KyleSimkus/TinyPowerController/TPC/Default Configuration/Outputs/3D Top Angle.png

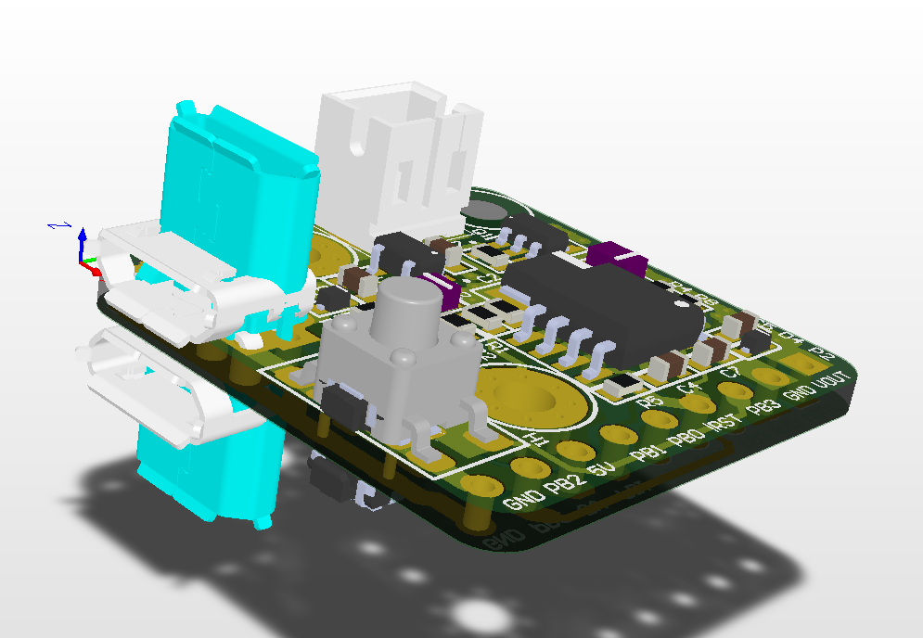
TPC/Default Configuration/Outputs/3D Top Angle.png
