KyleSimkus/TinyPowerController/TPC/Default Configuration/Outputs/3D Bottom.png

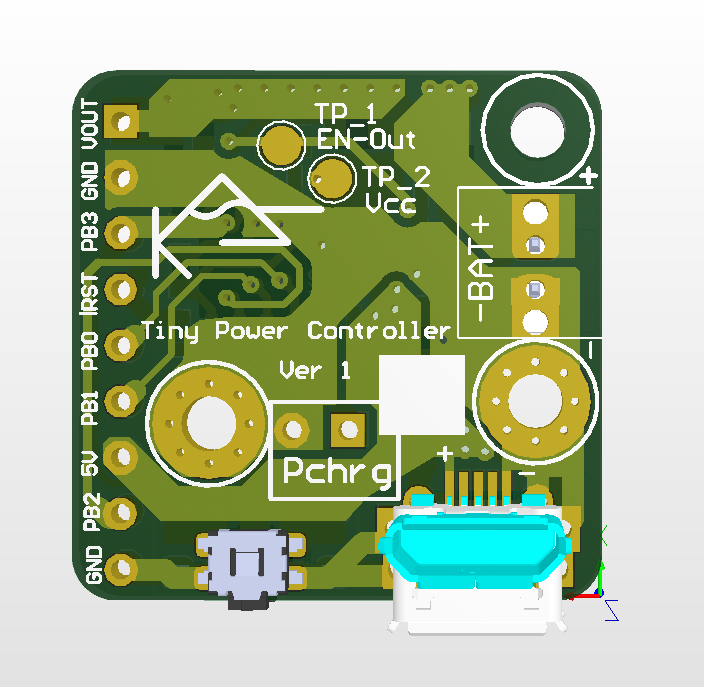
TPC/Default Configuration/Outputs/3D Bottom.png
