KyleSimkus/TinyPowerController/TPC/Default Configuration/Outputs/3D Top.png

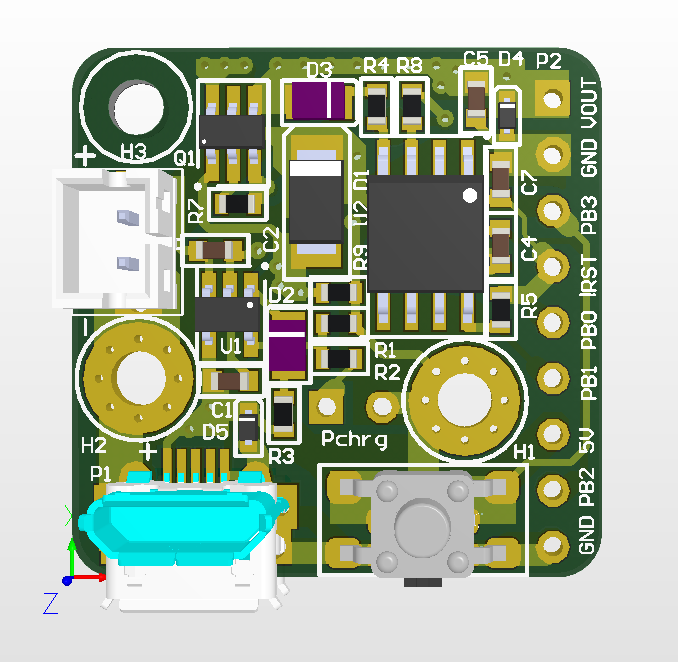
TPC/Default Configuration/Outputs/3D Top.png
